oleveque/PiWebcam/RaspberryPi/serveur/down-arrow.png

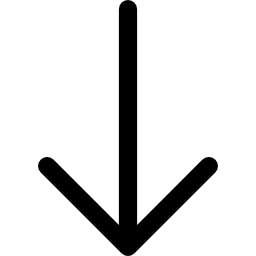
RaspberryPi/serveur/down-arrow.png
