oleveque/PiWebcam/RaspberryPi/serveur/left-arrow.png

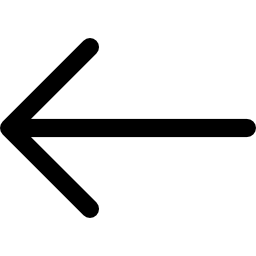
RaspberryPi/serveur/left-arrow.png
