oleveque/PiWebcam/RaspberryPi/serveur/left-roulis.png

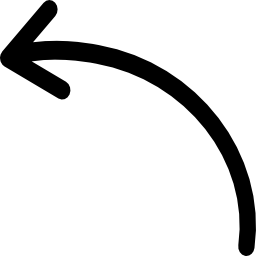
RaspberryPi/serveur/left-roulis.png
