oleveque/PiWebcam/RaspberryPi/serveur/power.png

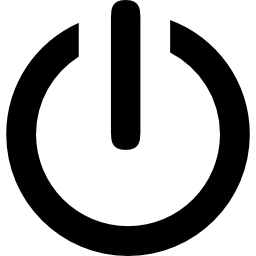
RaspberryPi/serveur/power.png
