oleveque/PiWebcam/RaspberryPi/serveur/reload.png

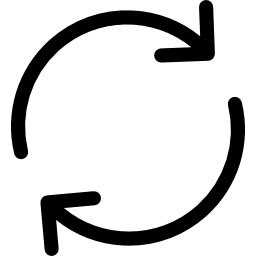
RaspberryPi/serveur/reload.png
