oleveque/PiWebcam/RaspberryPi/serveur/right-arrow.png

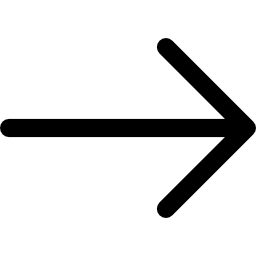
RaspberryPi/serveur/right-arrow.png
