oleveque/PiWebcam/RaspberryPi/serveur/up-arrow.png

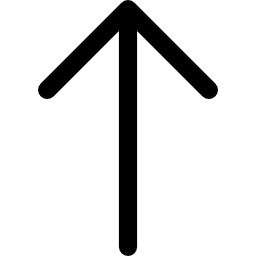
RaspberryPi/serveur/up-arrow.png
