oleveque/PiWebcam/RaspberryPi/serveur/zoom-in.png

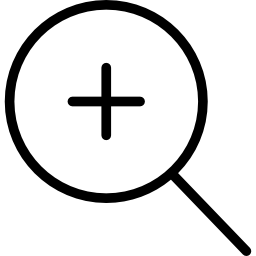
RaspberryPi/serveur/zoom-in.png
