oleveque/PiWebcam/RaspberryPi/serveur/zoom-out.png

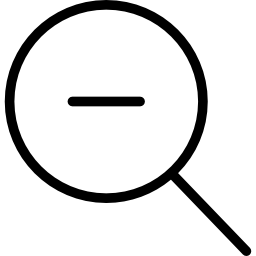
RaspberryPi/serveur/zoom-out.png
