oleveque/PiWebcam/Ressources/EtageAlimentation/IMG_20170320_134002.jpg

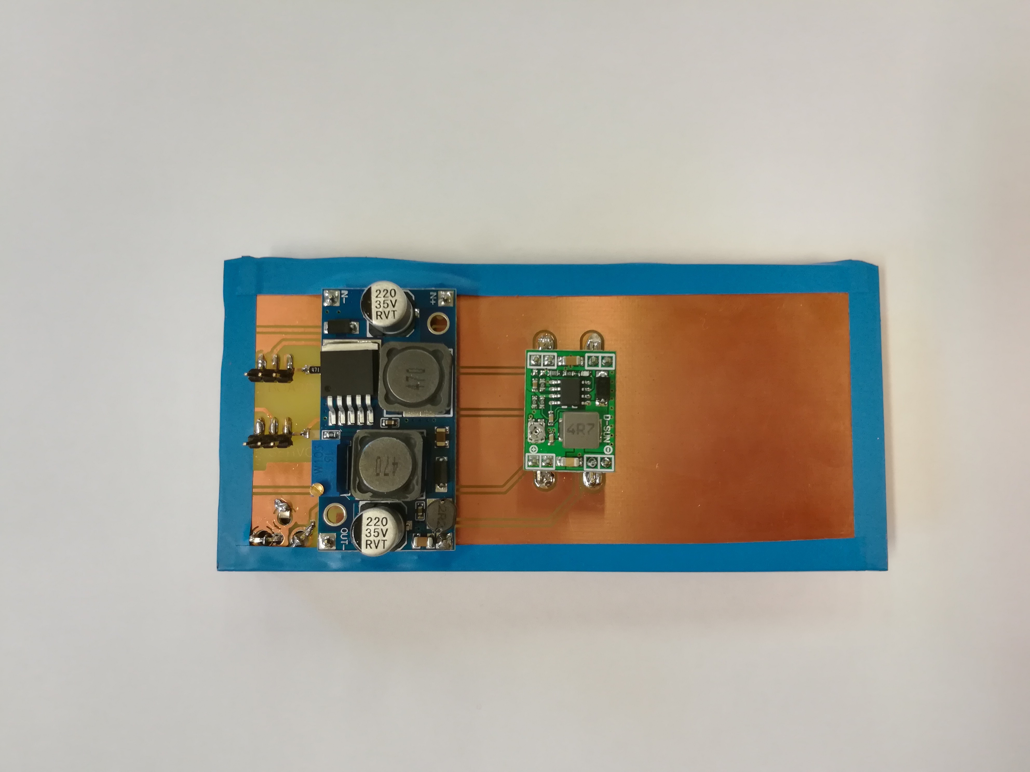
Ressources/EtageAlimentation/IMG_20170320_134002.jpg
