oleveque/PiWebcam/Ressources/EtageAlimentation/IMG_20170320_134050.jpg

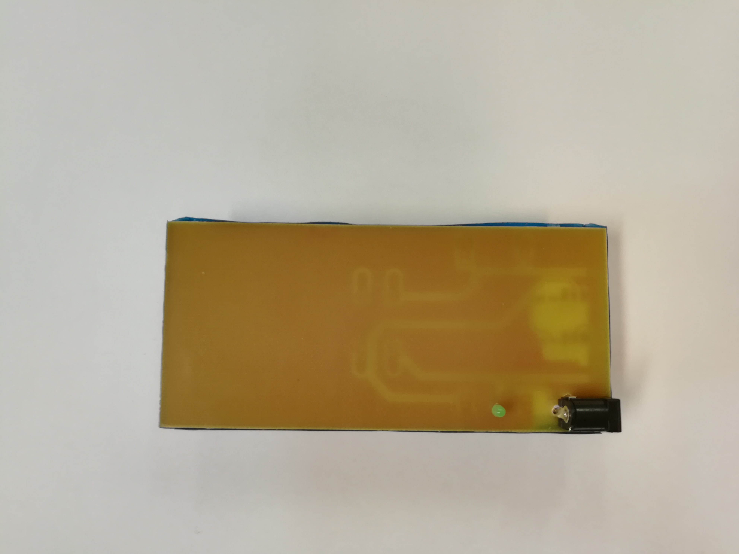
Ressources/EtageAlimentation/IMG_20170320_134050.jpg
